Hanbo-Hanbo/TAIL/Project_Images/2.JPG

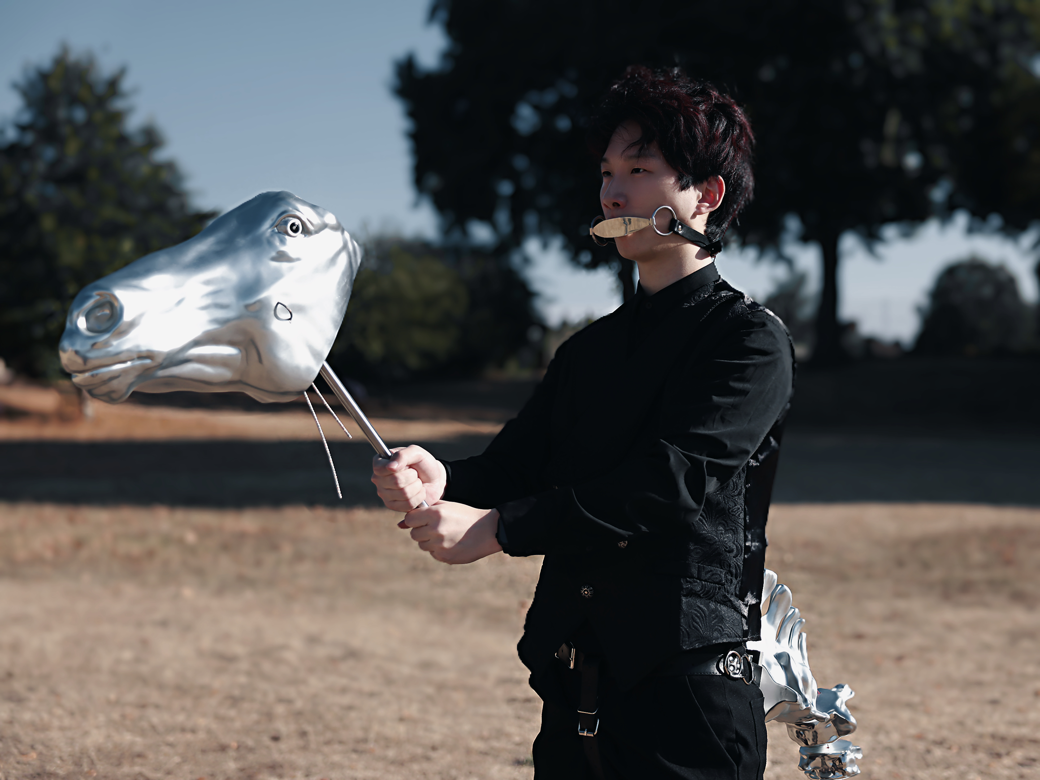
Project_Images/2.JPG
