Hanbo-Hanbo/TAIL/Project_Images/4.JPG

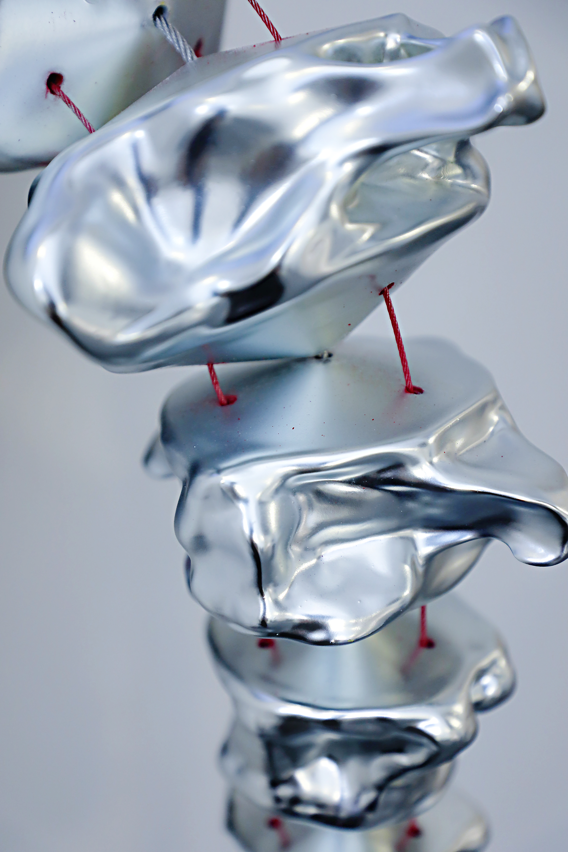
Project_Images/4.JPG
