Hanbo-Hanbo/TAIL/Project_Images/5.JPG

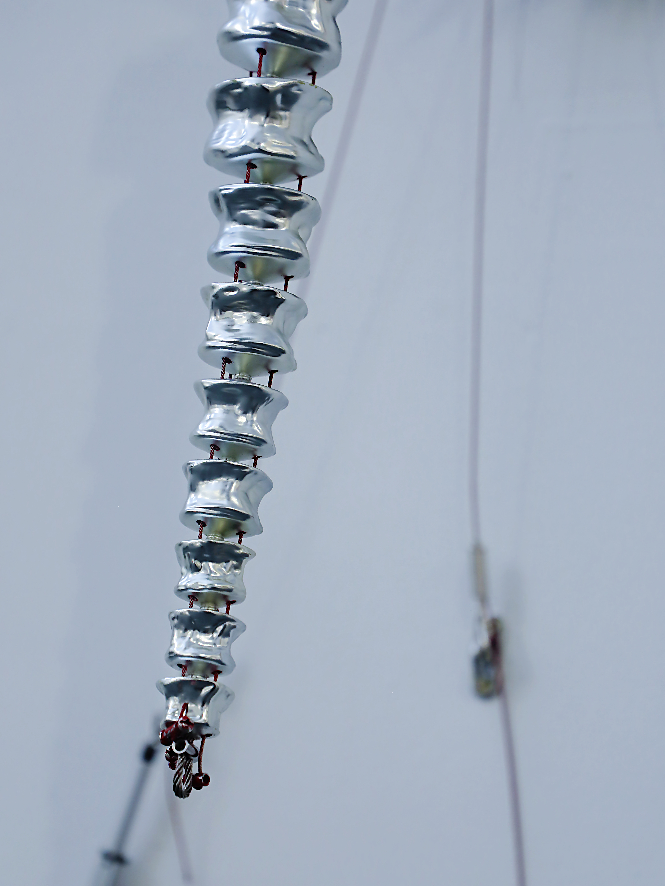
Project_Images/5.JPG
